dieseltravis/travis-ergogen-numpad/kle/travis-ergonum.jpg

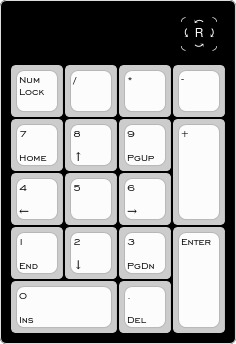
kle/travis-ergonum.jpg
