dieseltravis/travis-ergogen-numpad/output/cases/plate.stl

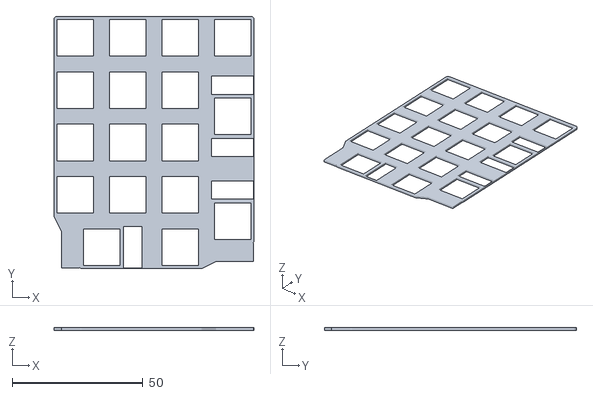
[picture p20: CAD file, 2024-04-24]
output/cases/plate.stl
76.6 x 96.6 x 1.00
