dieseltravis/travis-ergogen-numpad/output/outlines/plate.dxf

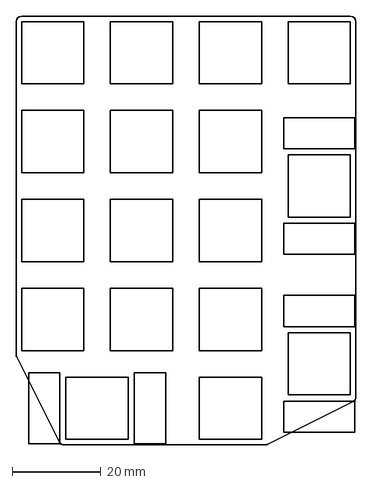
[picture p21: CAD file, 2024-04-24]
output/outlines/plate.dxf
76.6 x 96.6 mm
