dieseltravis/travis-ergogen-numpad/output/cases/_outerWall.stl

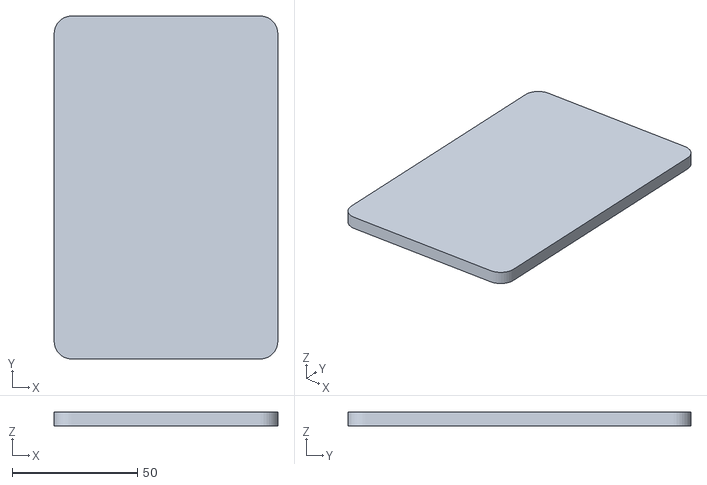
[picture p22: CAD file, 2024-04-14]
output/cases/_outerWall.stl
89.2 x 136.8 x 5.60
