dieseltravis/travis-ergogen-numpad/output/outlines/2u_stabilizer.dxf

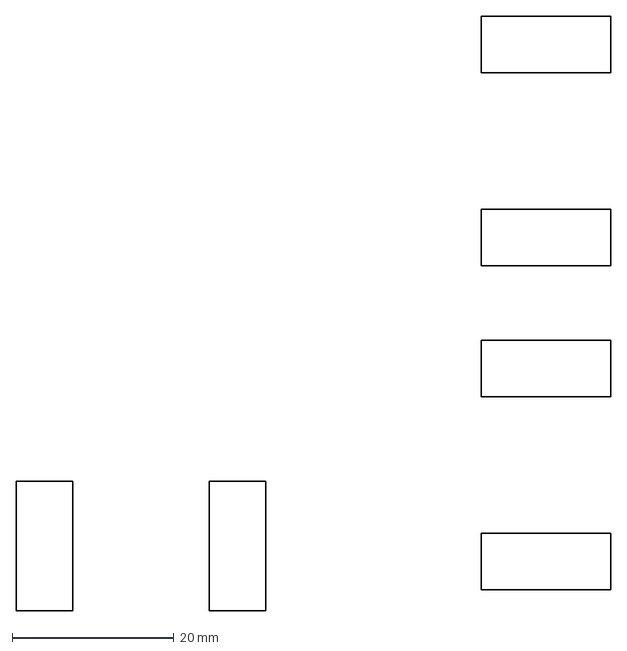
[picture p23: CAD file, 2024-04-24]
output/outlines/2u_stabilizer.dxf
73.6 x 73.6 mm
