dieseltravis/travis-ergogen-numpad/output/cases/xlBottom.stl

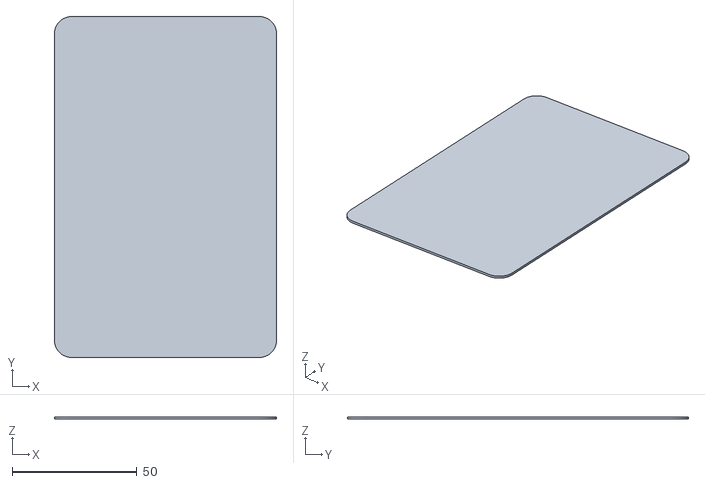
[picture p24: CAD file, 2024-04-14]
output/cases/xlBottom.stl
89.2 x 136.8 x 1.00
