dieseltravis/travis-ergogen-numpad/output/outlines/keyholes.dxf

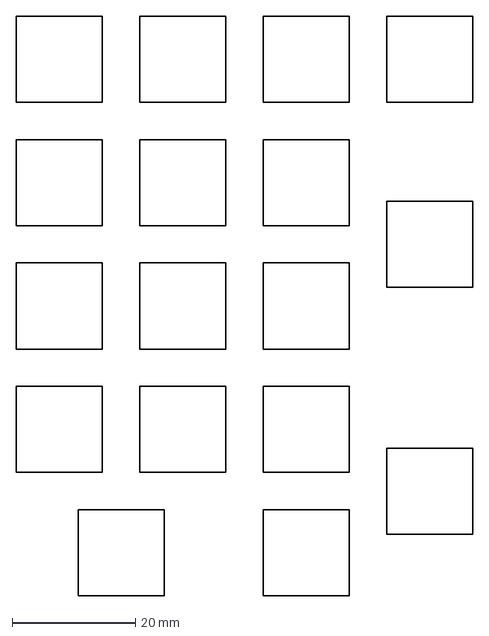
[picture p25: CAD file, 2024-04-14]
output/outlines/keyholes.dxf
74.2 x 94.2 mm
