dieseltravis/travis-ergogen-numpad/output/outlines/smBoard.dxf

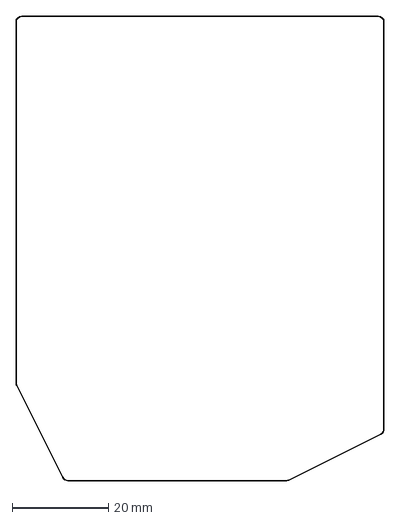
[picture p26: CAD file, 2024-04-14]
output/outlines/smBoard.dxf
76.6 x 96.6 mm
