dieseltravis/travis-ergogen-numpad/output/outlines/xlBoard.dxf

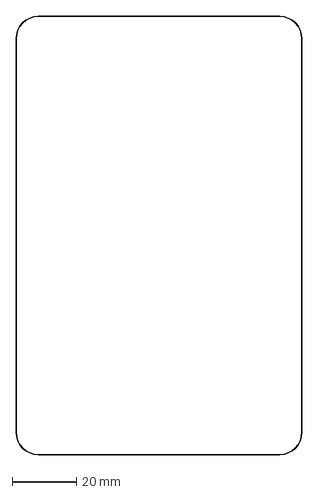
[picture p27: CAD file, 2024-04-14]
output/outlines/xlBoard.dxf
89.2 x 136.8 mm
