dieseltravis/travis-ergogen-numpad/output/outlines/_raw.dxf

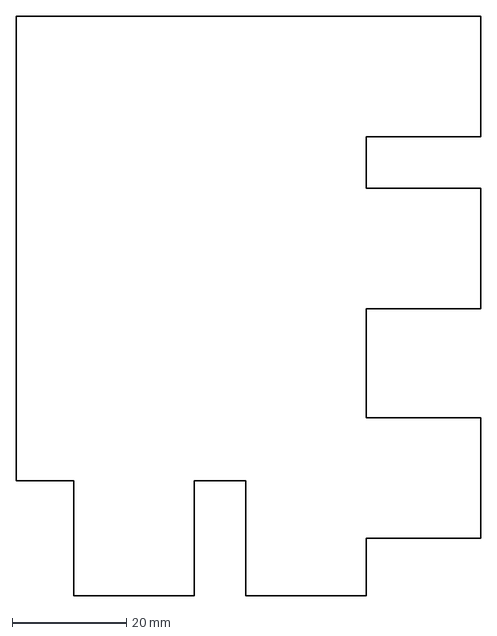
[picture p28: CAD file, 2024-04-10]
output/outlines/_raw.dxf
81.2 x 101.2 mm
