dieseltravis/travis-ergogen-numpad/output/outlines/keys.dxf

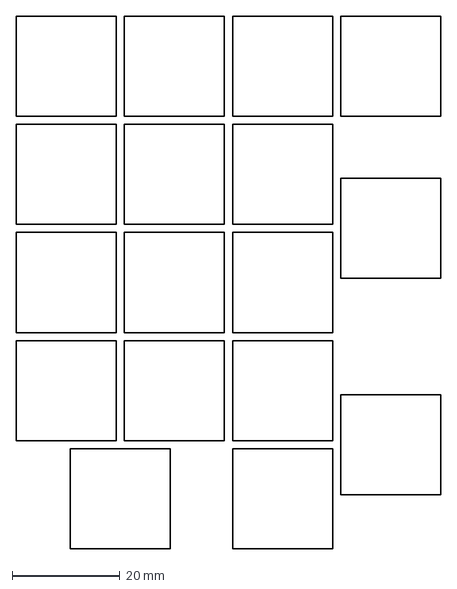
[picture p29: CAD file, 2024-04-09]
output/outlines/keys.dxf
78.7 x 98.8 mm
