dieseltravis/travis-ergogen-numpad/kbplacer/travis_num2024.kicad_sch

## KiCad design kbplacer/travis_num2024.kicad_sch (2024-07-14)

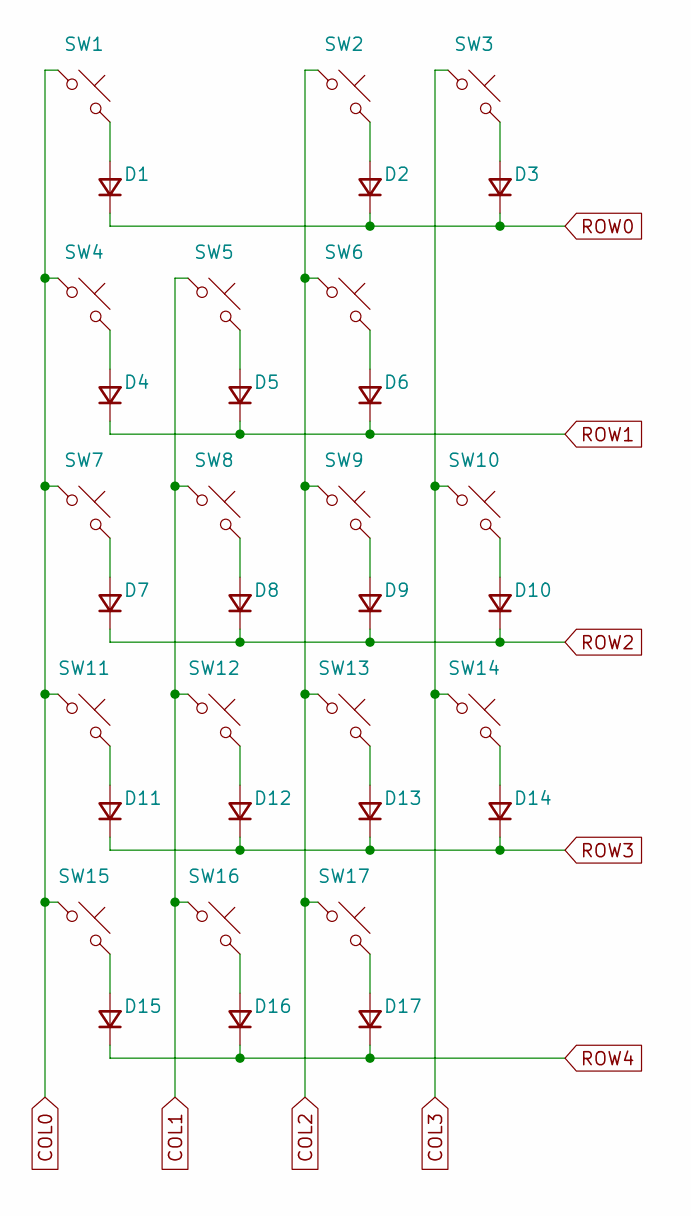
[picture p38: schematic travis_num2024.kicad_sch]

Parts:
D1, D2, D3, D4, D5, D6, D7, D8, D9, D10, D11, D12, D13, D14, D15, D16, D17: D
SW1, SW2, SW3, SW4, SW5, SW6, SW7, SW8, SW9, SW10, SW11, SW12, SW13, SW14, SW15, SW16, SW17: SW_Push

Connections:
COL0: SW1.1, SW4.1, SW7.1, SW11.1, SW15.1
COL1: SW5.1, SW8.1, SW12.1, SW16.1
COL2: SW2.1, SW6.1, SW9.1, SW13.1, SW17.1
COL3: SW3.1, SW10.1, SW14.1
unnamed: D1.2 (A), SW1.2
unnamed: D2.2 (A), SW2.2
unnamed: D3.2 (A), SW3.2
unnamed: D4.2 (A), SW4.2
unnamed: D5.2 (A), SW5.2
unnamed: D6.2 (A), SW6.2
unnamed: D7.2 (A), SW7.2
unnamed: D8.2 (A), SW8.2
unnamed: D9.2 (A), SW9.2
unnamed: D10.2 (A), SW10.2
unnamed: D11.2 (A), SW11.2
unnamed: D12.2 (A), SW12.2
unnamed: D13.2 (A), SW13.2
unnamed: D14.2 (A), SW14.2
unnamed: D15.2 (A), SW15.2
unnamed: D16.2 (A), SW16.2
unnamed: D17.2 (A), SW17.2
ROW0: D1.1 (K), D2.1 (K), D3.1 (K)
ROW1: D4.1 (K), D5.1 (K), D6.1 (K)
ROW2: D7.1 (K), D8.1 (K), D9.1 (K), D10.1 (K)
ROW3: D11.1 (K), D12.1 (K), D13.1 (K), D14.1 (K)
ROW4: D15.1 (K), D16.1 (K), D17.1 (K)
