dieseltravis/travis-ergogen-numpad/output/points/points.yaml

matrix_col0_row0:
    x: 50.025
    'y': -200
    r: 0
    meta:
        stagger: 0
        spread: 20.05
        splay: 0
        origin:
            - 0
            - 0
        orient: 0
        shift:
            - 10.025
            - 0
        rotate: 0
        adjust: {}
        width: 38.1
        height: 18.05
        padding: 20.05
        autobind: 10
        skip: false
        asym: both
        colrow: col0_row0
        name: matrix_col0_row0
        column_net: col0
        tags:
            - key
            - 2u_stabilizers
            - row_even
        row_net: row0
        key:
            led_next: ''
            led_this: LED_20
        zone:
            key:
                padding: kp
                spread: kp
            columns:
                col0:
                    key:
                        column_net: col0
                    rows:
                        row0:
                            width: 2U
                            shift:
                                - 0.5kp
                                - 0
                            tags:
                                - key
                                - 2u_stabilizers
                                - row_even
                            key:
                                led_next: ''
                                led_this: LED_20
                        row1:
                            shift:
                                - '-0.5kp'
                                - 0
                            key:
                                led_next: LED_16
                                led_this: LED_15
                        row2:
                            key:
                                led_next: LED_15
                                led_this: LED_14
                        row3:
                            key:
                                led_next: LED_9
                                led_this: LED_8
                        row4:
                            key:
                                led_next: LED_8
                                led_this: LED_7
                    name: col0
                col1:
                    key:
                        column_net: col1
                    rows:
                        row0:
                            skip: true
                        row1:
                            key:
                                led_next: LED_17
                                led_this: LED_16
                        row2:
                            key:
                                led_next: LED_14
                                led_this: LED_13
                        row3:
                            key:
                                led_next: LED_10
                                led_this: LED_9
                        row4:
                            key:
                                led_next: LED_7
                                led_this: LED_6
                    name: col1
                col2:
                    key:
                        column_net: col2
                    rows:
                        row0:
                            key:
                                led_next: LED_20
                                led_this: LED_19
                        row1:
                            key:
                                led_next: LED_18
                                led_this: LED_17
                        row2:
                            key:
                                led_next: LED_13
                                led_this: LED_12
                        row3:
                            key:
                                led_next: LED_11
                                led_this: LED_10
                        row4:
                            key:
                                led_next: LED_6
                                led_this: LED_5
                    name: col2
                col3:
                    key:
                        column_net: col3
                    rows:
                        row0:
                            shift:
                                - 0
                                - 0.5kp
                            rotate: 90
                            width: 2U
                            tags:
                                - key
                                - 2u_stabilizers
                                - row_even
                            key:
                                led_next: LED_19
                                led_this: LED_18
                        row1:
                            rotate: -90
                            shift:
                                - 1kp
                                - '-1kp'
                            skip: true
                        row2:
                            rotate: 90
                            width: 2U
                            tags:
                                - key
                                - 2u_stabilizers
                                - row_even
                            key:
                                led_next: LED_12
                                led_this: LED_11
                        row3:
                            rotate: -90
                            shift:
                                - 0.5kp
                                - '-1kp'
                            skip: true
                        row4:
                            row_net: row3
                            key:
                                led_next: LED_5
                                led_this: LED_4
                    name: col3
            rows:
                row0:
                    tags:
                        - key
                        - row_even
                    row_net: row0
                row1:
                    tags:
                        - key
                        - row_odd
                    row_net: row1
                row2:
                    tags:
                        - key
                        - row_even
                    row_net: row2
                row3:
                    tags:
                        - key
                        - row_odd
                    row_net: row3
                row4:
                    tags:
                        - key
                        - row_even
                    row_net: row4
            name: matrix
        col:
            key:
                column_net: col0
            rows:
                row0:
                    width: 2U
                    shift:
                        - 0.5kp
                        - 0
                    tags:
                        - key
                        - 2u_stabilizers
                        - row_even
                    key:
                        led_next: ''
                        led_this: LED_20
                row1:
                    shift:
                        - '-0.5kp'
                        - 0
                    key:
                        led_next: LED_16
                        led_this: LED_15
                row2:
                    key:
                        led_next: LED_15
                        led_this: LED_14
                row3:
                    key:
                        led_next: LED_9
                        led_this: LED_8
                row4:
                    key:
                        led_next: LED_8
                        led_this: LED_7
            name: col0
        row: row0
        bind:
            - 10
            - 0
            - 0
            - 0
matrix_col0_row1:
    x: 40
    'y': -179.95
    r: 0
    meta:
        stagger: 0
        spread: 20.05
        splay: 0
        origin:
            - 0
            - 0
        orient: 0
        shift:
            - -10.025
            - 0
        rotate: 0
        adjust: {}
        width: 18.05
        height: 18.05
        padding: 20.05
        autobind: 10
        skip: false
        asym: both
        colrow: col0_row1
        name: matrix_col0_row1
        column_net: col0
        tags:
            - key
            - row_odd
        row_net: row1
        key:
            led_next: LED_16
            led_this: LED_15
        zone:
            key:
                padding: kp
                spread: kp
            columns:
                col0:
                    key:
                        column_net: col0
                    rows:
                        row0:
                            width: 2U
                            shift:
                                - 0.5kp
                                - 0
                            tags:
                                - key
                                - 2u_stabilizers
                                - row_even
                            key:
                                led_next: ''
                                led_this: LED_20
                        row1:
                            shift:
                                - '-0.5kp'
                                - 0
                            key:
                                led_next: LED_16
                                led_this: LED_15
                        row2:
                            key:
                                led_next: LED_15
                                led_this: LED_14
                        row3:
                            key:
                                led_next: LED_9
                                led_this: LED_8
                        row4:
                            key:
                                led_next: LED_8
                                led_this: LED_7
                    name: col0
                col1:
                    key:
                        column_net: col1
                    rows:
                        row0:
                            skip: true
                        row1:
                            key:
                                led_next: LED_17
                                led_this: LED_16
                        row2:
                            key:
                                led_next: LED_14
                                led_this: LED_13
                        row3:
                            key:
                                led_next: LED_10
                                led_this: LED_9
                        row4:
                            key:
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
                        led_next: LED_16
                        led_this: LED_15
                row2:
                    key:
                        led_next: LED_15
                        led_this: LED_14
                row3:
                    key:
                        led_next: LED_9
                        led_this: LED_8
                row4:
                    key:
                        led_next: LED_8
                        led_this: LED_7
            name: col0
        row: row1
        bind:
            - 10
            - 10
            - 10
            - 0
matrix_col0_row2:
    x: 40
    'y': -159.89999999999998
    r: 0
    meta:
        stagger: 0
        spread: 20.05
        splay: 0
        origin:
            - 0
            - 0
        orient: 0
        shift:
            - 0
            - 0
        rotate: 0
        adjust: {}
        width: 18.05
        height: 18.05
        padding: 20.05
        autobind: 10
        skip: false
        asym: both
        colrow: col0_row2
        name: matrix_col0_row2
        column_net: col0
        tags:
            - key
            - row_even
        row_net: row2
        key:
            led_next: LED_15
            led_this: LED_14
        zone:
            key:
                padding: kp
                spread: kp
            columns:
                col0:
                    key:
                        column_net: col0
                    rows:
                        row0:
                            width: 2U
                            shift:
                                - 0.5kp
                                - 0
                            tags:
                                - key
                                - 2u_stabilizers
                                - row_even
                            key:
                                led_next: ''
                                led_this: LED_20
                        row1:
                            shift:
                                - '-0.5kp'
                                - 0
                            key:
                                led_next: LED_16
                                led_this: LED_15
                        row2:
                            key:
                                led_next: LED_15
                                led_this: LED_14
                        row3:
                            key:
                                led_next: LED_9
                                led_this: LED_8
                        row4:
                            key:
                                led_next: LED_8
                                led_this: LED_7
                    name: col0
                col1:
                    key:
                        column_net: col1
                    rows:
                        row0:
                            skip: true
                        row1:
                            key:
                                led_next: LED_17
                                led_this: LED_16
                        row2:
                            key:
                                led_next: LED_14
                                led_this: LED_13
                        row3:
                            key:
                                led_next: LED_10
                                led_this: LED_9
                        row4:
                            key:
                                led_next: LED_7
                                led_this: LED_6
                    name: col1
                col2:
                    key:
                        column_net: col2
                    rows:
                        row0:
                            key:
                                led_next: LED_20
                                led_this: LED_19
                        row1:
                            key:
                                led_next: LED_18
                                led_this: LED_17
                        row2:
                            key:
                                led_next: LED_13
                                led_this: LED_12
                        row3:
                            key:
                                led_next: LED_11
                                led_this: LED_10
                        row4:
                            key:
                                led_next: LED_6
                                led_this: LED_5
                    name: col2
                col3:
                    key:
                        column_net: col3
                    rows:
                        row0:
                            shift:
                                - 0
                                - 0.5kp
                            rotate: 90
                            width: 2U
                            tags:
                                - key
                                - 2u_stabilizers
                                - row_even
                            key:
                                led_next: LED_19
                                led_this: LED_18
                        row1:
                            rotate: -90
                            shift:
                                - 1kp
                                - '-1kp'
                            skip: true
                        row2:
                            rotate: 90
                            width: 2U
                            tags:
                                - key
                                - 2u_stabilizers
                                - row_even
                            key:
                                led_next: LED_12
                                led_this: LED_11
                        row3:
                            rotate: -90
                            shift:
                                - 0.5kp
                                - '-1kp'
                            skip: true
                        row4:
                            row_net: row3
                            key:
                                led_next: LED_5
                                led_this: LED_4
                    name: col3
            rows:
                row0:
                    tags:
                        - key
                        - row_even
                    row_net: row0
                row1:
                    tags:
                        - key
                        - row_odd
                    row_net: row1
                row2:
                    tags:
                        - key
                        - row_even
                    row_net: row2
                row3:
                    tags:
                        - key
                        - row_odd
                    row_net: row3
                row4:
                    tags:
                        - key
                        - row_even
                    row_net: row4
            name: matrix
        col:
            key:
                column_net: col0
            rows:
                row0:
                    width: 2U
                    shift:
                        - 0.5kp
                        - 0
                    tags:
                        - key
                        - 2u_stabilizers
                        - row_even
                    key:
                        led_next: ''
                        led_this: LED_20
                row1:
                    shift:
                        - '-0.5kp'
                        - 0
                    key:
                        led_next: LED_16
                        led_this: LED_15
                row2:
                    key:
                        led_next: LED_15
                        led_this: LED_14
                row3:
                    key:
                        led_next: LED_9
                        led_this: LED_8
                row4:
                    key:
                        led_next: LED_8
                        led_this: LED_7
            name: col0
        row: row2
        bind:
            - 10
            - 10
            - 10
            - 0
matrix_col0_row3:
    x: 40
    'y': -139.84999999999997
    r: 0
    meta:
        stagger: 0
        spread: 20.05
        splay: 0
        origin:
            - 0
            - 0
        orient: 0
        shift:
            - 0
            - 0
        rotate: 0
        adjust: {}
        width: 18.05
        height: 18.05
        padding: 20.05
        autobind: 10
        skip: false
        asym: both
        colrow: col0_row3
        name: matrix_col0_row3
        column_net: col0
        tags:
            - key
            - row_odd
        row_net: row3
        key:
            led_next: LED_9
            led_this: LED_8
        zone:
            key:
                padding: kp
                spread: kp
            columns:
                col0:
                    key:
                        column_net: col0
                    rows:
                        row0:
                            width: 2U
                            shift:
                                - 0.5kp
                                - 0
                            tags:
                                - key
                                - 2u_stabilizers
                                - row_even
                            key:
                                led_next: ''
                                led_this: LED_20
                        row1:
                            shift:
                                - '-0.5kp'
                                - 0
                            key:
                                led_next: LED_16
                                led_this: LED_15
                        row2:
                            key:
                                led_next: LED_15
                                led_this: LED_14
                        row3:
                            key:
                                led_next: LED_9
                                led_this: LED_8
                        row4:
                            key:
                                led_next: LED_8
                                led_this: LED_7
                    name: col0
                col1:
                    key:
                        column_net: col1
                    rows:
                        row0:
                            skip: true
                        row1:
                            key:
                                led_next: LED_17
                                led_this: LED_16
                        row2:
                            key:
                                led_next: LED_14
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
                    key:
                        led_next: ''
                        led_this: LED_20
                row1:
                    shift:
                        - '-0.5kp'
                        - 0
                    key:
                        led_next: LED_16
                        led_this: LED_15
                row2:
                    key:
                        led_next: LED_15
                        led_this: LED_14
                row3:
                    key:
                        led_next: LED_9
                        led_this: LED_8
                row4:
                    key:
                        led_next: LED_8
                        led_this: LED_7
            name: col0
        row: row3
        bind:
            - 10
            - 10
            - 10
            - 0
matrix_col0_row4:
    x: 40
    'y': -119.79999999999997
    r: 0
    meta:
        stagger: 0
        spread: 20.05
        splay: 0
        origin:
            - 0
            - 0
        orient: 0
        shift:
            - 0
            - 0
        rotate: 0
        adjust: {}
        width: 18.05
        height: 18.05
        padding: 20.05
        autobind: 10
        skip: false
        asym: both
        colrow: col0_row4
        name: matrix_col0_row4
        column_net: col0
        tags:
            - key
            - row_even
        row_net: row4
        key:
            led_next: LED_8
            led_this: LED_7
        zone:
            key:
                padding: kp
                spread: kp
            columns:
                col0:
                    key:
                        column_net: col0
                    rows:
                        row0:
                            width: 2U
                            shift:
                                - 0.5kp
                                - 0
                            tags:
                                - key
                                - 2u_stabilizers
                                - row_even
                            key:
                                led_next: ''
                                led_this: LED_20
                        row1:
                            shift:
                                - '-0.5kp'
                                - 0
                            key:
                                led_next: LED_16
                                led_this: LED_15
                        row2:
                            key:
                                led_next: LED_15
                                led_this: LED_14
                        row3:
                            key:
                                led_next: LED_9
                                led_this: LED_8
                        row4:
                            key:
                                led_next: LED_8
                                led_this: LED_7
                    name: col0
                col1:
                    key:
                        column_net: col1
                    rows:
                        row0:
                            skip: true
                        row1:
                            key:
                                led_next: LED_17
                                led_this: LED_16
                        row2:
                            key:
                                led_next: LED_14
                                led_this: LED_13
                        row3:
                            key:
                                led_next: LED_10
                                led_this: LED_9
                        row4:
                            key:
                                led_next: LED_7
                                led_this: LED_6
                    name: col1
                col2:
                    key:
                        column_net: col2
                    rows:
                        row0:
                            key:
                                led_next: LED_20
                                led_this: LED_19
                        row1:
                            key:
                                led_next: LED_18
                                led_this: LED_17
                        row2:
                            key:
                                led_next: LED_13
                                led_this: LED_12
                        row3:
                            key:
                                led_next: LED_11
                                led_this: LED_10
                        row4:
                            key:
                                led_next: LED_6
                                led_this: LED_5
                    name: col2
                col3:
                    key:
                        column_net: col3
                    rows:
                        row0:
                            shift:
                                - 0
                                - 0.5kp
                            rotate: 90
                            width: 2U
                            tags:
                                - key
                                - 2u_stabilizers
                                - row_even
                            key:
                                led_next: LED_19
                                led_this: LED_18
                        row1:
                            rotate: -90
                            shift:
                                - 1kp
                                - '-1kp'
                            skip: true
                        row2:
                            rotate: 90
                            width: 2U
                            tags:
                                - key
                                - 2u_stabilizers
                                - row_even
                            key:
                                led_next: LED_12
                                led_this: LED_11
                        row3:
                            rotate: -90
                            shift:
                                - 0.5kp
                                - '-1kp'
                            skip: true
                        row4:
                            row_net: row3
                            key:
                                led_next: LED_5
                                led_this: LED_4
                    name: col3
            rows:
                row0:
                    tags:
                        - key
                        - row_even
                    row_net: row0
                row1:
                    tags:
                        - key
                        - row_odd
                    row_net: row1
                row2:
                    tags:
                        - key
                        - row_even
                    row_net: row2
                row3:
                    tags:
                        - key
                        - row_odd
                    row_net: row3
                row4:
                    tags:
                        - key
                        - row_even
                    row_net: row4
            name: matrix
        col:
            key:
                column_net: col0
            rows:
                row0:
                    width: 2U
                    shift:
                        - 0.5kp
                        - 0
                    tags:
                        - key
                        - 2u_stabilizers
                        - row_even
                    key:
                        led_next: ''
                        led_this: LED_20
                row1:
                    shift:
                        - '-0.5kp'
                        - 0
                    key:
                        led_next: LED_16
                        led_this: LED_15
                row2:
                    key:
                        led_next: LED_15
                        led_this: LED_14
                row3:
                    key:
                        led_next: LED_9
                        led_this: LED_8
                row4:
                    key:
                        led_next: LED_8
                        led_this: LED_7
            name: col0
        row: row4
        bind:
            - 0
            - 10
            - 10
            - 0
matrix_col1_row1:
    x: 60.05
    'y': -179.95
    r: 0
    meta:
        stagger: 0
        spread: 20.05
        splay: 0
        origin:
            - 0
            - 0
        orient: 0
        shift:
            - 0
            - 0
        rotate: 0
        adjust: {}
        width: 18.05
        height: 18.05
        padding: 20.05
        autobind: 10
        skip: false
        asym: both
        colrow: col1_row1
        name: matrix_col1_row1
        column_net: col1
        tags:
            - key
            - row_odd
        row_net: row1
        key:
            led_next: LED_17
            led_this: LED_16
        zone:
            key:
                padding: kp
                spread: kp
            columns:
                col0:
                    key:
                        column_net: col0
                    rows:
                        row0:
                            width: 2U
                            shift:
                                - 0.5kp
                                - 0
                            tags:
                                - key
                                - 2u_stabilizers
                                - row_even
                            key:
                                led_next: ''
                                led_this: LED_20
                        row1:
                            shift:
                                - '-0.5kp'
                                - 0
                            key:
                                led_next: LED_16
                                led_this: LED_15
                        row2:
                            key:
                                led_next: LED_15
                                led_this: LED_14
                        row3:
                            key:
                                led_next: LED_9
                                led_this: LED_8
                        row4:
                            key:
                                led_next: LED_8
                                led_this: LED_7
                    name: col0
                col1:
                    key:
                        column_net: col1
                    rows:
                        row0:
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
            rows:
                row0:
                    skip: true
                row1:
                    key:
                        led_next: LED_17
                        led_this: LED_16
                row2:
                    key:
                        led_next: LED_14
                        led_this: LED_13
                row3:
                    key:
                        led_next: LED_10
                        led_this: LED_9
                row4:
                    key:
                        led_next: LED_7
                        led_this: LED_6
            name: col1
        row: row1
        bind:
            - 10
            - 10
            - 0
            - 10
matrix_col1_row2:
    x: 60.05
    'y': -159.89999999999998
    r: 0
    meta:
        stagger: 0
        spread: 20.05
        splay: 0
        origin:
            - 0
            - 0
        orient: 0
        shift:
            - 0
            - 0
        rotate: 0
        adjust: {}
        width: 18.05
        height: 18.05
        padding: 20.05
        autobind: 10
        skip: false
        asym: both
        colrow: col1_row2
        name: matrix_col1_row2
        column_net: col1
        tags:
            - key
            - row_even
        row_net: row2
        key:
            led_next: LED_14
            led_this: LED_13
        zone:
            key:
                padding: kp
                spread: kp
            columns:
                col0:
                    key:
                        column_net: col0
                    rows:
                        row0:
                            width: 2U
                            shift:
                                - 0.5kp
                                - 0
                            tags:
                                - key
                                - 2u_stabilizers
                                - row_even
                            key:
                                led_next: ''
                                led_this: LED_20
                        row1:
                            shift:
                                - '-0.5kp'
                                - 0
                            key:
                                led_next: LED_16
                                led_this: LED_15
                        row2:
                            key:
                                led_next: LED_15
                                led_this: LED_14
                        row3:
                            key:
                                led_next: LED_9
                                led_this: LED_8
                        row4:
                            key:
                                led_next: LED_8
                                led_this: LED_7
                    name: col0
                col1:
                    key:
                        column_net: col1
                    rows:
                        row0:
                            skip: true
                        row1:
                            key:
                                led_next: LED_17
                                led_this: LED_16
                        row2:
                            key:
                                led_next: LED_14
                                led_this: LED_13
                        row3:
                            key:
                                led_next: LED_10
                                led_this: LED_9
                        row4:
                            key:
                                led_next: LED_7
                                led_this: LED_6
                    name: col1
                col2:
                    key:
                        column_net: col2
                    rows:
                        row0:
                            key:
                                led_next: LED_20
                                led_this: LED_19
                        row1:
                            key:
                                led_next: LED_18
                                led_this: LED_17
                        row2:
                            key:
                                led_next: LED_13
                                led_this: LED_12
                        row3:
                            key:
                                led_next: LED_11
                                led_this: LED_10
                        row4:
                            key:
                                led_next: LED_6
                                led_this: LED_5
                    name: col2
                col3:
                    key:
                        column_net: col3
                    rows:
                        row0:
                            shift:
                                - 0
                                - 0.5kp
                            rotate: 90
                            width: 2U
                            tags:
                                - key
                                - 2u_stabilizers
                                - row_even
                            key:
                                led_next: LED_19
                                led_this: LED_18
                        row1:
                            rotate: -90
                            shift:
                                - 1kp
                                - '-1kp'
                            skip: true
                        row2:
                            rotate: 90
                            width: 2U
                            tags:
                                - key
                                - 2u_stabilizers
                                - row_even
                            key:
                                led_next: LED_12
                                led_this: LED_11
                        row3:
                            rotate: -90
                            shift:
                                - 0.5kp
                                - '-1kp'
                            skip: true
                        row4:
                            row_net: row3
                            key:
                                led_next: LED_5
                                led_this: LED_4
                    name: col3
            rows:
                row0:
                    tags:
                        - key
                        - row_even
                    row_net: row0
                row1:
                    tags:
                        - key
                        - row_odd
                    row_net: row1
                row2:
                    tags:
                        - key
                        - row_even
                    row_net: row2
                row3:
                    tags:
                        - key
                        - row_odd
                    row_net: row3
                row4:
                    tags:
                        - key
                        - row_even
                    row_net: row4
            name: matrix
        col:
            key:
                column_net: col1
            rows:
                row0:
                    skip: true
                row1:
                    key:
                        led_next: LED_17
                        led_this: LED_16
                row2:
                    key:
                        led_next: LED_14
                        led_this: LED_13
                row3:
                    key:
                        led_next: LED_10
                        led_this: LED_9
                row4:
                    key:
                        led_next: LED_7
                        led_this: LED_6
            name: col1
        row: row2
        bind:
            - 10
            - 10
            - 10
            - 10
matrix_col1_row3:
    x: 60.05
    'y': -139.84999999999997
    r: 0
    meta:
        stagger: 0
        spread: 20.05
        splay: 0
        origin:
            - 0
            - 0
        orient: 0
        shift:
            - 0
            - 0
        rotate: 0
        adjust: {}
        width: 18.05
        height: 18.05
        padding: 20.05
        autobind: 10
        skip: false
        asym: both
        colrow: col1_row3
        name: matrix_col1_row3
        column_net: col1
        tags:
            - key
            - row_odd
        row_net: row3
        key:
            led_next: LED_10
            led_this: LED_9
        zone:
            key:
                padding: kp
                spread: kp
            columns:
                col0:
                    key:
                        column_net: col0
                    rows:
                        row0:
                            width: 2U
                            shift:
                                - 0.5kp
                                - 0
                            tags:
                                - key
                                - 2u_stabilizers
                                - row_even
                            key:
                                led_next: ''
                                led_this: LED_20
                        row1:
                            shift:
                                - '-0.5kp'
                                - 0
                            key:
                                led_next: LED_16
                                led_this: LED_15
                        row2:
                            key:
                                led_next: LED_15
                                led_this: LED_14
                        row3:
                            key:
                                led_next: LED_9
                                led_this: LED_8
                        row4:
                            key:
                                led_next: LED_8
                                led_this: LED_7
                    name: col0
                col1:
                    key:
                        column_net: col1
                    rows:
                        row0:
                            skip: true
                        row1:
                            key:
                                led_next: LED_17
                                led_this: LED_16
                        row2:
                            key:
                                led_next: LED_14
                                led_this: LED_13
                        row3:
                            key:
                                led_next: LED_10
                                led_this: LED_9
                        row4:
                            key:
                                led_next: LED_7
                                led_this: LED_6
                    name: col1
                col2:
                    key:
                        column_net: col2
                    rows:
                        row0:
                            key:
                                led_next: LED_20
                                led_this: LED_19
                        row1:
                            key:
                                led_next: LED_18
                                led_this: LED_17
                        row2:
                            key:
                                led_next: LED_13
                                led_this: LED_12
                        row3:
                            key:
                                led_next: LED_11
                                led_this: LED_10
                        row4:
                            key:
                                led_next: LED_6
                                led_this: LED_5
                    name: col2
                col3:
                    key:
                        column_net: col3
                    rows:
                        row0:
                            shift:
                                - 0
                                - 0.5kp
                            rotate: 90
                            width: 2U
                            tags:
                                - key
                                - 2u_stabilizers
                                - row_even
                            key:
                                led_next: LED_19
                                led_this: LED_18
                        row1:
                            rotate: -90
                            shift:
                                - 1kp
                                - '-1kp'
                            skip: true
                        row2:
                            rotate: 90
                            width: 2U
                            tags:
                                - key
                                - 2u_stabilizers
                                - row_even
                            key:
                                led_next: LED_12
                                led_this: LED_11
                        row3:
                            rotate: -90
                            shift:
                                - 0.5kp
                                - '-1kp'
                            skip: true
                        row4:
                            row_net: row3
                            key:
                                led_next: LED_5
                                led_this: LED_4
                    name: col3
            rows:
                row0:
                    tags:
                        - key
                        - row_even
                    row_net: row0
                row1:
                    tags:
                        - key
                        - row_odd
                    row_net: row1
                row2:
                    tags:
                        - key
                        - row_even
                    row_net: row2
                row3:
                    tags:
                        - key
                        - row_odd
                    row_net: row3
                row4:
                    tags:
                        - key
                        - row_even
                    row_net: row4
            name: matrix
        col:
            key:
                column_net: col1
            rows:
                row0:
                    skip: true
                row1:
                    key:
                        led_next: LED_17
                        led_this: LED_16
                row2:
                    key:
                        led_next: LED_14
                        led_this: LED_13
                row3:
                    key:
                        led_next: LED_10
                        led_this: LED_9
                row4:
                    key:
                        led_next: LED_7
                        led_this: LED_6
            name: col1
        row: row3
        bind:
            - 10
            - 10
            - 10
            - 10
matrix_col1_row4:
    x: 60.05
    'y': -119.79999999999997
    r: 0
    meta:
        stagger: 0
        spread: 20.05
        splay: 0
        origin:
            - 0
            - 0
        orient: 0
        shift:
            - 0
            - 0
        rotate: 0
        adjust: {}
        width: 18.05
        height: 18.05
        padding: 20.05
        autobind: 10
        skip: false
        asym: both
        colrow: col1_row4
        name: matrix_col1_row4
        column_net: col1
        tags:
            - key
            - row_even
        row_net: row4
        key:
            led_next: LED_7
            led_this: LED_6
        zone:
            key:
                padding: kp
                spread: kp
            columns:
                col0:
                    key:
                        column_net: col0
                    rows:
                        row0:
                            width: 2U
                            shift:
                                - 0.5kp
                                - 0
                            tags:
                                - key
                                - 2u_stabilizers
                                - row_even
                            key:
                                led_next: ''
                                led_this: LED_20
                        row1:
                            shift:
                                - '-0.5kp'
                                - 0
                            key:
                                led_next: LED_16
                                led_this: LED_15
                        row2:
                            key:
                                led_next: LED_15
                                led_this: LED_14
                        row3:
                            key:
                                led_next: LED_9
                                led_this: LED_8
                        row4:
                            key:
                                led_next: LED_8
                                led_this: LED_7
                    name: col0
                col1:
                    key:
                        column_net: col1
                    rows:
                        row0:
                            skip: true
                        row1:
                            key:
                                led_next: LED_17
                                led_this: LED_16
                        row2:
                            key:
                                led_next: LED_14
                                led_this: LED_13
                        row3:
                            key:
                                led_next: LED_10
                                led_this: LED_9
                        row4:
                            key:
                                led_next: LED_7
                                led_this: LED_6
                    name: col1
                col2:
                    key:
                        column_net: col2
                    rows:
                        row0:
                            key:
                                led_next: LED_20
                                led_this: LED_19
                        row1:
                            key:
                                led_next: LED_18
                                led_this: LED_17
                        row2:
                            key:
                                led_next: LED_13
                                led_this: LED_12
                        row3:
                            key:
                                led_next: LED_11
                                led_this: LED_10
                        row4:
                            key:
                                led_next: LED_6
                                led_this: LED_5
                    name: col2
                col3:
                    key:
                        column_net: col3
                    rows:
                        row0:
                            shift:
                                - 0
                                - 0.5kp
                            rotate: 90
                            width: 2U
                            tags:
                                - key
                                - 2u_stabilizers
                                - row_even
                            key:
                                led_next: LED_19
                                led_this: LED_18
                        row1:
                            rotate: -90
                            shift:
                                - 1kp
                                - '-1kp'
                            skip: true
                        row2:
                            rotate: 90
                            width: 2U
                            tags:
                                - key
                                - 2u_stabilizers
                                - row_even
                            key:
                                led_next: LED_12
                                led_this: LED_11
                        row3:
                            rotate: -90
                            shift:
                                - 0.5kp
                                - '-1kp'
                            skip: true
                        row4:
                            row_net: row3
                            key:
                                led_next: LED_5
                                led_this: LED_4
                    name: col3
            rows:
                row0:
                    tags:
                        - key
                        - row_even
                    row_net: row0
                row1:
                    tags:
                        - key
                        - row_odd
                    row_net: row1
                row2:
                    tags:
                        - key
                        - row_even
                    row_net: row2
                row3:
                    tags:
                        - key
                        - row_odd
                    row_net: row3
                row4:
                    tags:
                        - key
                        - row_even
                    row_net: row4
            name: matrix
        col:
            key:
                column_net: col1
            rows:
                row0:
                    skip: true
                row1:
                    key:
                        led_next: LED_17
                        led_this: LED_16
                row2:
                    key:
                        led_next: LED_14
                        led_this: LED_13
                row3:
                    key:
                        led_next: LED_10
                        led_this: LED_9
                row4:
                    key:
                        led_next: LED_7
                        led_this: LED_6
            name: col1
        row: row4
        bind:
            - 0
            - 10
            - 10
            - 10
matrix_col2_row0:
    x: 80.1
    'y': -200
    r: 0
    meta:
        stagger: 0
        spread: 20.05
        splay: 0
        origin:
            - 0
            - 0
        orient: 0
        shift:
            - 0
            - 0
        rotate: 0
        adjust: {}
        width: 18.05
        height: 18.05
        padding: 20.05
        autobind: 10
        skip: false
        asym: both
        colrow: col2_row0
        name: matrix_col2_row0
        column_net: col2
        tags:
            - key
            - row_even
        row_net: row0
        key:
            led_next: LED_20
            led_this: LED_19
        zone:
            key:
                padding: kp
                spread: kp
            columns:
                col0:
                    key:
                        column_net: col0
                    rows:
                        row0:
                            width: 2U
                            shift:
                                - 0.5kp
                                - 0
                            tags:
                                - key
                                - 2u_stabilizers
                                - row_even
                            key:
                                led_next: ''
                                led_this: LED_20
                        row1:
                            shift:
                                - '-0.5kp'
                                - 0
                            key:
                                led_next: LED_16
                                led_this: LED_15
                        row2:
                            key:
                                led_next: LED_15
                                led_this: LED_14
                        row3:
                            key:
                                led_next: LED_9
                                led_this: LED_8
                        row4:
                            key:
                                led_next: LED_8
                                led_this: LED_7
                    name: col0
                col1:
                    key:
                        column_net: col1
                    rows:
                        row0:
                            skip: true
                        row1:
                            key:
                                led_next: LED_17
                                led_this: LED_16
                        row2:
                            key:
                                led_next: LED_14
                                led_this: LED_13
                        row3:
                            key:
                                led_next: LED_10
                                led_this: LED_9
                        row4:
                            key:
                                led_next: LED_7
                                led_this: LED_6
                    name: col1
                col2:
                    key:
                        column_net: col2
                    rows:
                        row0:
                            key:
                                led_next: LED_20
                                led_this: LED_19
                        row1:
                            key:
                                led_next: LED_18
                                led_this: LED_17
                        row2:
                            key:
                                led_next: LED_13
                                led_this: LED_12
                        row3:
                            key:
                                led_next: LED_11
                                led_this: LED_10
                        row4:
                            key:
                                led_next: LED_6
                                led_this: LED_5
                    name: col2
                col3:
                    key:
                        column_net: col3
                    rows:
                        row0:
                            shift:
                                - 0
                                - 0.5kp
                            rotate: 90
                            width: 2U
                            tags:
                                - key
                                - 2u_stabilizers
                                - row_even
                            key:
                                led_next: LED_19
                                led_this: LED_18
                        row1:
                            rotate: -90
                            shift:
                                - 1kp
                                - '-1kp'
                            skip: true
                        row2:
                            rotate: 90
                            width: 2U
                            tags:
                                - key
                                - 2u_stabilizers
                                - row_even
                            key:
                                led_next: LED_12
                                led_this: LED_11
                        row3:
                            rotate: -90
                            shift:
                                - 0.5kp
                                - '-1kp'
                            skip: true
                        row4:
                            row_net: row3
                            key:
                                led_next: LED_5
                                led_this: LED_4
                    name: col3
            rows:
                row0:
                    tags:
                        - key
                        - row_even
                    row_net: row0
                row1:
                    tags:
                        - key
                        - row_odd
                    row_net: row1
                row2:
                    tags:
                        - key
                        - row_even
                    row_net: row2
                row3:
                    tags:
                        - key
                        - row_odd
                    row_net: row3
                row4:
                    tags:
                        - key
                        - row_even
                    row_net: row4
            name: matrix
        col:
            key:
                column_net: col2
            rows:
                row0:
                    key:
                        led_next: LED_20
                        led_this: LED_19
                row1:
                    key:
                        led_next: LED_18
                        led_this: LED_17
                row2:
                    key:
                        led_next: LED_13
                        led_this: LED_12
                row3:
                    key:
                        led_next: LED_11
                        led_this: LED_10
                row4:
                    key:
                        led_next: LED_6
                        led_this: LED_5
            name: col2
        row: row0
        bind:
            - 10
            - 0
            - 0
            - 0
matrix_col2_row1:
    x: 80.1
    'y': -179.95
    r: 0
    meta:
        stagger: 0
        spread: 20.05
        splay: 0
        origin:
            - 0
            - 0
        orient: 0
        shift:
            - 0
            - 0
        rotate: 0
        adjust: {}
        width: 18.05
        height: 18.05
        padding: 20.05
        autobind: 10
        skip: false
        asym: both
        colrow: col2_row1
        name: matrix_col2_row1
        column_net: col2
        tags:
            - key
            - row_odd
        row_net: row1
        key:
            led_next: LED_18
            led_this: LED_17
        zone:
            key:
                padding: kp
                spread: kp
            columns:
                col0:
                    key:
                        column_net: col0
                    rows:
                        row0:
                            width: 2U
                            shift:
                                - 0.5kp
                                - 0
                            tags:
                                - key
                                - 2u_stabilizers
                                - row_even
                            key:
                                led_next: ''
                                led_this: LED_20
                        row1:
                            shift:
                                - '-0.5kp'
                                - 0
                            key:
                                led_next: LED_16
                                led_this: LED_15
                        row2:
                            key:
                                led_next: LED_15
                                led_this: LED_14
                        row3:
                            key:
                                led_next: LED_9
                                led_this: LED_8
                        row4:
                            key:
                                led_next: LED_8
                                led_this: LED_7
                    name: col0
                col1:
                    key:
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
                    row_net: row4
            name: matrix
        col:
            key:
                column_net: col2
            rows:
                row0:
                    key:
                        led_next: LED_20
                        led_this: LED_19
                row1:
                    key:
                        led_next: LED_18
                        led_this: LED_17
                row2:
                    key:
                        led_next: LED_13
                        led_this: LED_12
                row3:
                    key:
                        led_next: LED_11
                        led_this: LED_10
                row4:
                    key:
                        led_next: LED_6
                        led_this: LED_5
            name: col2
        row: row1
        bind:
            - 10
            - 10
            - 10
            - 10
matrix_col2_row2:
    x: 80.1
    'y': -159.89999999999998
    r: 0
    meta:
        stagger: 0
        spread: 20.05
        splay: 0
        origin:
            - 0
            - 0
        orient: 0
        shift:
            - 0
            - 0
        rotate: 0
        adjust: {}
        width: 18.05
        height: 18.05
        padding: 20.05
        autobind: 10
        skip: false
        asym: both
        colrow: col2_row2
        name: matrix_col2_row2
        column_net: col2
        tags:
            - key
            - row_even
        row_net: row2
        key:
            led_next: LED_13
            led_this: LED_12
        zone:
            key:
                padding: kp
                spread: kp
            columns:
                col0:
                    key:
                        column_net: col0
                    rows:
                        row0:
                            width: 2U
                            shift:
                                - 0.5kp
                                - 0
                            tags:
                                - key
                                - 2u_stabilizers
                                - row_even
                            key:
                                led_next: ''
                                led_this: LED_20
                        row1:
                            shift:
                                - '-0.5kp'
                                - 0
                            key:
                                led_next: LED_16
                                led_this: LED_15
                        row2:
                            key:
                                led_next: LED_15
                                led_this: LED_14
                        row3:
                            key:
                                led_next: LED_9
                                led_this: LED_8
                        row4:
                            key:
                                led_next: LED_8
                                led_this: LED_7
                    name: col0
                col1:
                    key:
                        column_net: col1
                    rows:
                        row0:
                            skip: true
                        row1:
                            key:
                                led_next: LED_17
                                led_this: LED_16
                        row2:
                            key:
                                led_next: LED_14
                                led_this: LED_13
                        row3:
                            key:
                                led_next: LED_10
                                led_this: LED_9
                        row4:
                            key:
                                led_next: LED_7
                                led_this: LED_6
                    name: col1
                col2:
                    key:
                        column_net: col2
                    rows:
                        row0:
                            key:
                                led_next: LED_20
                                led_this: LED_19
                        row1:
                            key:
                                led_next: LED_18
                                led_this: LED_17
                        row2:
                            key:
                                led_next: LED_13
                                led_this: LED_12
                        row3:
                            key:
                                led_next: LED_11
                                led_this: LED_10
                        row4:
                            key:
                                led_next: LED_6
                                led_this: LED_5
                    name: col2
                col3:
                    key:
                        column_net: col3
                    rows:
                        row0:
                            shift:
                                - 0
                                - 0.5kp
                            rotate: 90
                            width: 2U
                            tags:
                                - key
                                - 2u_stabilizers
                                - row_even
                            key:
                                led_next: LED_19
                                led_this: LED_18
                        row1:
                            rotate: -90
                            shift:
                                - 1kp
                                - '-1kp'
                            skip: true
                        row2:
                            rotate: 90
                            width: 2U
                            tags:
                                - key
                                - 2u_stabilizers
                                - row_even
                            key:
                                led_next: LED_12
                                led_this: LED_11
                        row3:
                            rotate: -90
                            shift:
                                - 0.5kp
                                - '-1kp'
                            skip: true
                        row4:
                            row_net: row3
                            key:
                                led_next: LED_5
                                led_this: LED_4
                    name: col3
            rows:
                row0:
                    tags:
                        - key
                        - row_even
                    row_net: row0
                row1:
                    tags:
                        - key
                        - row_odd
                    row_net: row1
                row2:
                    tags:
                        - key
                        - row_even
                    row_net: row2
                row3:
                    tags:
                        - key
                        - row_odd
                    row_net: row3
                row4:
                    tags:
                        - key
                        - row_even
                    row_net: row4
            name: matrix
        col:
            key:
                column_net: col2
            rows:
                row0:
                    key:
                        led_next: LED_20
                        led_this: LED_19
                row1:
                    key:
                        led_next: LED_18
                        led_this: LED_17
                row2:
                    key:
                        led_next: LED_13
                        led_this: LED_12
                row3:
                    key:
                        led_next: LED_11
                        led_this: LED_10
                row4:
                    key:
                        led_next: LED_6
                        led_this: LED_5
            name: col2
        row: row2
        bind:
            - 10
            - 10
            - 10
            - 10
matrix_col2_row3:
    x: 80.1
    'y': -139.84999999999997
    r: 0
    meta:
        stagger: 0
        spread: 20.05
        splay: 0
        origin:
            - 0
            - 0
        orient: 0
        shift:
            - 0
            - 0
        rotate: 0
        adjust: {}
        width: 18.05
        height: 18.05
        padding: 20.05
        autobind: 10
        skip: false
        asym: both
        colrow: col2_row3
        name: matrix_col2_row3
        column_net: col2
        tags:
            - key
            - row_odd
        row_net: row3
        key:
            led_next: LED_11
            led_this: LED_10
        zone:
            key:
                padding: kp
                spread: kp
            columns:
                col0:
                    key:
                        column_net: col0
                    rows:
                        row0:
                            width: 2U
                            shift:
                                - 0.5kp
                                - 0
                            tags:
                                - key
                                - 2u_stabilizers
                                - row_even
                            key:
                                led_next: ''
                                led_this: LED_20
                        row1:
                            shift:
                                - '-0.5kp'
                                - 0
                            key:
                                led_next: LED_16
                                led_this: LED_15
                        row2:
                            key:
                                led_next: LED_15
                                led_this: LED_14
                        row3:
                            key:
                                led_next: LED_9
                                led_this: LED_8
                        row4:
                            key:
                                led_next: LED_8
                                led_this: LED_7
                    name: col0
                col1:
                    key:
                        column_net: col1
                    rows:
                        row0:
                            skip: true
                        row1:
                            key:
                                led_next: LED_17
                                led_this: LED_16
                        row2:
                            key:
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
                row2:
                    key:
                        led_next: LED_13
                        led_this: LED_12
                row3:
                    key:
                        led_next: LED_11
                        led_this: LED_10
                row4:
                    key:
                        led_next: LED_6
                        led_this: LED_5
            name: col2
        row: row3
        bind:
            - 10
            - 10
            - 10
            - 10
matrix_col2_row4:
    x: 80.1
    'y': -119.79999999999997
    r: 0
    meta:
        stagger: 0
        spread: 20.05
        splay: 0
        origin:
            - 0
            - 0
        orient: 0
        shift:
            - 0
            - 0
        rotate: 0
        adjust: {}
        width: 18.05
        height: 18.05
        padding: 20.05
        autobind: 10
        skip: false
        asym: both
        colrow: col2_row4
        name: matrix_col2_row4
        column_net: col2
        tags:
            - key
            - row_even
        row_net: row4
        key:
            led_next: LED_6
            led_this: LED_5
        zone:
            key:
                padding: kp
                spread: kp
            columns:
                col0:
                    key:
                        column_net: col0
                    rows:
                        row0:
                            width: 2U
                            shift:
                                - 0.5kp
                                - 0
                            tags:
                                - key
                                - 2u_stabilizers
                                - row_even
                            key:
                                led_next: ''
                                led_this: LED_20
                        row1:
                            shift:
                                - '-0.5kp'
                                - 0
                            key:
                                led_next: LED_16
                                led_this: LED_15
                        row2:
                            key:
                                led_next: LED_15
                                led_this: LED_14
                        row3:
                            key:
                                led_next: LED_9
                                led_this: LED_8
                        row4:
                            key:
                                led_next: LED_8
                                led_this: LED_7
                    name: col0
                col1:
                    key:
                        column_net: col1
                    rows:
                        row0:
                            skip: true
                        row1:
                            key:
                                led_next: LED_17
                                led_this: LED_16
                        row2:
                            key:
                                led_next: LED_14
                                led_this: LED_13
                        row3:
                            key:
                                led_next: LED_10
                                led_this: LED_9
                        row4:
                            key:
                                led_next: LED_7
                                led_this: LED_6
                    name: col1
                col2:
                    key:
                        column_net: col2
                    rows:
                        row0:
                            key:
                                led_next: LED_20
                                led_this: LED_19
                        row1:
                            key:
                                led_next: LED_18
                                led_this: LED_17
                        row2:
                            key:
                                led_next: LED_13
                                led_this: LED_12
                        row3:
                            key:
                                led_next: LED_11
                                led_this: LED_10
                        row4:
                            key:
                                led_next: LED_6
                                led_this: LED_5
                    name: col2
                col3:
                    key:
                        column_net: col3
                    rows:
                        row0:
                            shift:
                                - 0
                                - 0.5kp
                            rotate: 90
                            width: 2U
                            tags:
                                - key
                                - 2u_stabilizers
                                - row_even
                            key:
                                led_next: LED_19
                                led_this: LED_18
                        row1:
                            rotate: -90
                            shift:
                                - 1kp
                                - '-1kp'
                            skip: true
                        row2:
                            rotate: 90
                            width: 2U
                            tags:
                                - key
                                - 2u_stabilizers
                                - row_even
                            key:
                                led_next: LED_12
                                led_this: LED_11
                        row3:
                            rotate: -90
                            shift:
                                - 0.5kp
                                - '-1kp'
                            skip: true
                        row4:
                            row_net: row3
                            key:
                                led_next: LED_5
                                led_this: LED_4
                    name: col3
            rows:
                row0:
                    tags:
                        - key
                        - row_even
                    row_net: row0
                row1:
                    tags:
                        - key
                        - row_odd
                    row_net: row1
                row2:
                    tags:
                        - key
                        - row_even
                    row_net: row2
                row3:
                    tags:
                        - key
                        - row_odd
                    row_net: row3
                row4:
                    tags:
                        - key
                        - row_even
                    row_net: row4
            name: matrix
        col:
            key:
                column_net: col2
            rows:
                row0:
                    key:
                        led_next: LED_20
                        led_this: LED_19
                row1:
                    key:
                        led_next: LED_18
                        led_this: LED_17
                row2:
                    key:
                        led_next: LED_13
                        led_this: LED_12
                row3:
                    key:
                        led_next: LED_11
                        led_this: LED_10
                row4:
                    key:
                        led_next: LED_6
                        led_this: LED_5
            name: col2
        row: row4
        bind:
            - 0
            - 10
            - 10
            - 10
matrix_col3_row0:
    x: 100.15
    'y': -189.975
    r: 90
    meta:
        stagger: 0
        spread: 20.05
        splay: 0
        origin:
            - 0
            - 0
        orient: 0
        shift:
            - 0
            - 10.025
        rotate: 90
        adjust: {}
        width: 38.1
        height: 18.05
        padding: 20.05
        autobind: 10
        skip: false
        asym: both
        colrow: col3_row0
        name: matrix_col3_row0
        column_net: col3
        tags:
            - key
            - 2u_stabilizers
            - row_even
        row_net: row0
        key:
            led_next: LED_19
            led_this: LED_18
        zone:
            key:
                padding: kp
                spread: kp
            columns:
                col0:
                    key:
                        column_net: col0
                    rows:
                        row0:
                            width: 2U
                            shift:
                                - 0.5kp
                                - 0
                            tags:
                                - key
                                - 2u_stabilizers
                                - row_even
                            key:
                                led_next: ''
                                led_this: LED_20
                        row1:
                            shift:
                                - '-0.5kp'
                                - 0
                            key:
                                led_next: LED_16
                                led_this: LED_15
                        row2:
                            key:
                                led_next: LED_15
                                led_this: LED_14
                        row3:
                            key:
                                led_next: LED_9
                                led_this: LED_8
                        row4:
                            key:
                                led_next: LED_8
                                led_this: LED_7
                    name: col0
                col1:
                    key:
                        column_net: col1
                    rows:
                        row0:
                            skip: true
                        row1:
                            key:
                                led_next: LED_17
                                led_this: LED_16
                        row2:
                            key:
                                led_next: LED_14
                                led_this: LED_13
                        row3:
                            key:
                                led_next: LED_10
                                led_this: LED_9
                        row4:
                            key:
                                led_next: LED_7
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
                    width: 2U
                    tags:
                        - key
                        - 2u_stabilizers
                        - row_even
                    key:
                        led_next: LED_12
                        led_this: LED_11
                row3:
                    rotate: -90
                    shift:
                        - 0.5kp
                        - '-1kp'
                    skip: true
                row4:
                    row_net: row3
                    key:
                        led_next: LED_5
                        led_this: LED_4
            name: col3
        row: row0
        bind:
            - 10
            - 0
            - 0
            - 10
matrix_col3_row2:
    x: 100.15
    'y': -149.87499999999997
    r: 90
    meta:
        stagger: 0
        spread: 20.05
        splay: 0
        origin:
            - 0
            - 0
        orient: 0
        shift:
            - 0
            - 0
        rotate: 90
        adjust: {}
        width: 38.1
        height: 18.05
        padding: 20.05
        autobind: 10
        skip: false
        asym: both
        colrow: col3_row2
        name: matrix_col3_row2
        column_net: col3
        tags:
            - key
            - 2u_stabilizers
            - row_even
        row_net: row2
        key:
            led_next: LED_12
            led_this: LED_11
        zone:
            key:
                padding: kp
                spread: kp
            columns:
                col0:
                    key:
                        column_net: col0
                    rows:
                        row0:
                            width: 2U
                            shift:
                                - 0.5kp
                                - 0
                            tags:
                                - key
                                - 2u_stabilizers
                                - row_even
                            key:
                                led_next: ''
                                led_this: LED_20
                        row1:
                            shift:
                                - '-0.5kp'
                                - 0
                            key:
                                led_next: LED_16
                                led_this: LED_15
                        row2:
                            key:
                                led_next: LED_15
                                led_this: LED_14
                        row3:
                            key:
                                led_next: LED_9
                                led_this: LED_8
                        row4:
                            key:
                                led_next: LED_8
                                led_this: LED_7
                    name: col0
                col1:
                    key:
                        column_net: col1
                    rows:
                        row0:
                            skip: true
                        row1:
                            key:
                                led_next: LED_17
                                led_this: LED_16
                        row2:
                            key:
                                led_next: LED_14
                                led_this: LED_13
                        row3:
                            key:
                                led_next: LED_10
                                led_this: LED_9
                        row4:
                            key:
                                led_next: LED_7
                                led_this: LED_6
                    name: col1
                col2:
                    key:
                        column_net: col2
                    rows:
                        row0:
                            key:
                                led_next: LED_20
                                led_this: LED_19
                        row1:
                            key:
                                led_next: LED_18
                                led_this: LED_17
                        row2:
                            key:
                                led_next: LED_13
                                led_this: LED_12
                        row3:
                            key:
                                led_next: LED_11
                                led_this: LED_10
                        row4:
                            key:
                                led_next: LED_6
                                led_this: LED_5
                    name: col2
                col3:
                    key:
                        column_net: col3
                    rows:
                        row0:
                            shift:
                                - 0
                                - 0.5kp
                            rotate: 90
                            width: 2U
                            tags:
                                - key
                                - 2u_stabilizers
                                - row_even
                            key:
                                led_next: LED_19
                                led_this: LED_18
                        row1:
                            rotate: -90
                            shift:
                                - 1kp
                                - '-1kp'
                            skip: true
                        row2:
                            rotate: 90
                            width: 2U
                            tags:
                                - key
                                - 2u_stabilizers
                                - row_even
                            key:
                                led_next: LED_12
                                led_this: LED_11
                        row3:
                            rotate: -90
                            shift:
                                - 0.5kp
                                - '-1kp'
                            skip: true
                        row4:
                            row_net: row3
                            key:
                                led_next: LED_5
                                led_this: LED_4
                    name: col3
            rows:
                row0:
                    tags:
                        - key
                        - row_even
                    row_net: row0
                row1:
                    tags:
                        - key
                        - row_odd
                    row_net: row1
                row2:
                    tags:
                        - key
                        - row_even
                    row_net: row2
                row3:
                    tags:
                        - key
                        - row_odd
                    row_net: row3
                row4:
                    tags:
                        - key
                        - row_even
                    row_net: row4
            name: matrix
        col:
            key:
                column_net: col3
            rows:
                row0:
                    shift:
                        - 0
                        - 0.5kp
                    rotate: 90
                    width: 2U
                    tags:
                        - key
                        - 2u_stabilizers
                        - row_even
                    key:
                        led_next: LED_19
                        led_this: LED_18
                row1:
                    rotate: -90
                    shift:
                        - 1kp
                        - '-1kp'
                    skip: true
                row2:
                    rotate: 90
                    width: 2U
                    tags:
                        - key
                        - 2u_stabilizers
                        - row_even
                    key:
                        led_next: LED_12
                        led_this: LED_11
                row3:
                    rotate: -90
                    shift:
                        - 0.5kp
                        - '-1kp'
                    skip: true
                row4:
                    row_net: row3
                    key:
                        led_next: LED_5
                        led_this: LED_4
            name: col3
        row: row2
        bind:
            - 10
            - 0
            - 10
            - 10
matrix_col3_row4:
    x: 100.15
    'y': -119.79999999999997
    r: 0
    meta:
        stagger: 0
        spread: 20.05
        splay: 0
        origin:
            - 0
            - 0
        orient: 0
        shift:
            - 0
            - 0
        rotate: 0
        adjust: {}
        width: 18.05
        height: 18.05
        padding: 20.05
        autobind: 10
        skip: false
        asym: both
        colrow: col3_row4
        name: matrix_col3_row4
        column_net: col3
        tags:
            - key
            - row_even
        row_net: row3
        key:
            led_next: LED_5
            led_this: LED_4
        zone:
            key:
                padding: kp
                spread: kp
            columns:
                col0:
                    key:
                        column_net: col0
                    rows:
                        row0:
                            width: 2U
                            shift:
                                - 0.5kp
                                - 0
                            tags:
                                - key
                                - 2u_stabilizers
                                - row_even
                            key:
                                led_next: ''
                                led_this: LED_20
                        row1:
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
