dieseltravis/travis-ergogen-numpad/output/outlines/plate.yaml

models:
    export:
        models:
            a:
                models:
                    a:
                        models:
                            a:
                                models:
                                    a:
                                        models: {}
                                        origin:
                                            - 0
                                            - 0
                                    b:
                                        models:
                                            a:
                                                models: {}
                                                origin:
                                                    - 0
                                                    - 0
                                            b:
                                                paths:
                                                    p1:
                                                        type: line
                                                        origin:
                                                            - 31.8
                                                            - -187.86671849999996
                                                        end:
                                                            - 31.8
                                                            - -112.79999999999997
                                                    p2:
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
                                    - -158.30499999999998
                                end:
                                    - 92.15
                                    - -165.30499999999998
                            ShapeLine4:
                                type: line
                                origin:
                                    - 92.15
                                    - -165.30499999999998
                                end:
                                    - 108.15
                                    - -165.30499999999998
                        origin:
                            - 0
                            - 0
                origin:
                    - 0
                    - 0
        origin:
            - 0
            - 0
units: mm
origin:
    - 0
    - 0
