dieseltravis/travis-ergogen-numpad/output/outlines/mounting.yaml

models:
    export:
        models:
            a:
                models:
                    a:
                        models:
                            a:
                                models:
                                    a:
                                        models: {}
                                        origin:
                                            - 0
                                            - 0
                                    b:
                                        paths:
                                            circle:
                                                type: circle
                                                origin:
                                                    - 30.975
                                                    - -78.46249999999998
                                                radius: 1.5
                                        origin:
                                            - 0
                                            - 0
                                origin:
                                    - 0
                                    - 0
                            b:
                                paths:
                                    circle:
                                        type: circle
                                        origin:
                                            - 109.17500000000001
                                            - -78.46249999999998
                                        radius: 1.5
                                origin:
                                    - 0
                                    - 0
                        origin:
                            - 0
                            - 0
                    b:
                        paths:
                            circle:
                                type: circle
                                origin:
                                    - 109.175
                                    - -209.025
                                radius: 1.5
                        origin:
                            - 0
                            - 0
                origin:
                    - 0
                    - 0
            b:
                paths:
                    circle:
                        type: circle
                        origin:
                            - 30.975
                            - -209.02499999999998
                        radius: 1.5
                origin:
                    - 0
                    - 0
        origin:
            - 0
            - 0
units: mm
origin:
    - 0
    - 0
