dieseltravis/travis-ergogen-numpad/output/points/units.yaml

U: 19.05
u: 19.05
cx: 18
cy: 17
$default_stagger: 0
$default_spread: 19.05
$default_splay: 0
$default_height: 18.05
$default_width: 18.05
$default_padding: 19.05
$default_autobind: 10
pp: 21.05
op: 25.05
kp: 20.05
smp: 1.2
xlp: 2
pw: 14
screwSize: 1.5
standoffSize: 3
top_y: 25.025
bot_y: -9.025
left_x: -9.025
right_x: 9.025
bt: 1
gt: 3
pt: 1.6
staby: 0
lblsize: 2.5
lblshift: -2.75
stabilizer_width: 7
stabilizer_height: 16
stabilizer_offset: 0
stabilizer_spacing_3u: 19.05
stabilizer_spacing_2u: 11.93
